Sch-ray/KUMA-DIV/Shell_Model/Image/IMG_3518.jpg

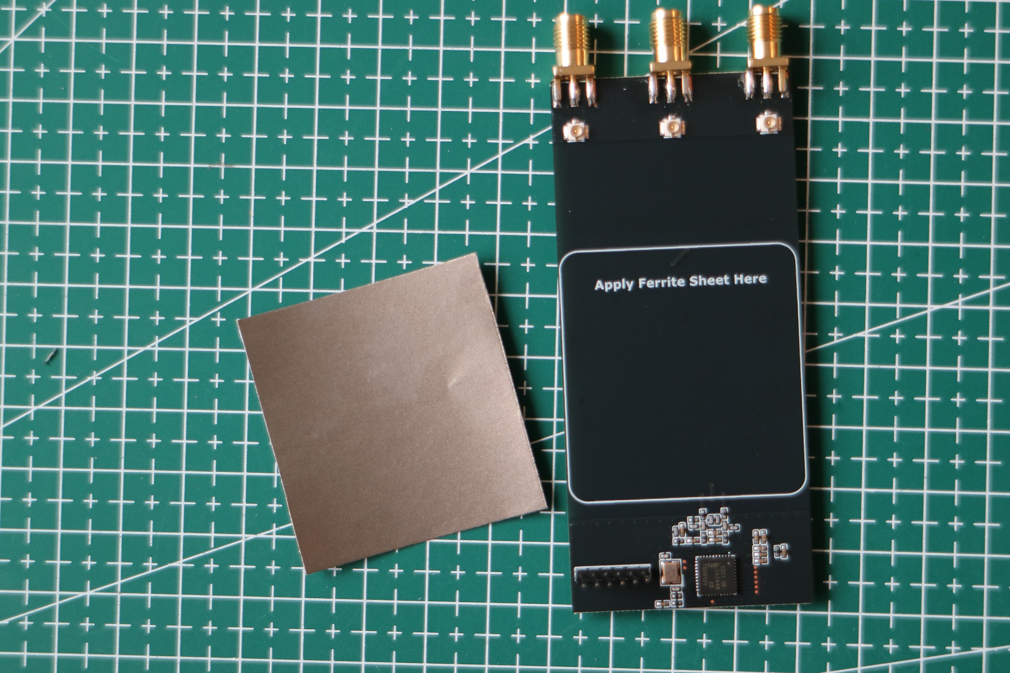
Shell_Model/Image/IMG_3518.jpg
