Sch-ray/KUMA-DIV/Software/ESP32-DIV/icon.h

// 'navigate_right2', 16x16px
const unsigned char bitmap_icon_navigate_right2 [] PROGMEM = {
	0x00, 0x00, 0x00, 0x00, 0x30, 0x80, 0x79, 0xc0, 0x3d, 0xe0, 0x1e, 0xf0, 0x0f, 0x7c, 0x07, 0xbe, 
	0x07, 0xbe, 0x0f, 0x7c, 0x1e, 0xf0, 0x3d, 0xe0, 0x79, 0xc0, 0x30, 0x80, 0x00, 0x00, 0x00, 0x00
};
// 'navigate_right', 16x16px
const unsigned char bitmap_icon_navigate_right [] PROGMEM = {
	0x00, 0x00, 0x00, 0x00, 0x06, 0x00, 0x0f, 0x00, 0x07, 0x80, 0x03, 0xc0, 0x01, 0xe0, 0x00, 0xf0, 
	0x00, 0xf0, 0x01, 0xe0, 0x03, 0xc0, 0x07, 0x80, 0x0f, 0x00, 0x06, 0x00, 0x00, 0x00, 0x00, 0x00
};
// 'navigate_left', 16x16px
const unsigned char bitmap_icon_navigate_left [] PROGMEM = {
	0x00, 0x00, 0x00, 0x00, 0x00, 0x60, 0x00, 0xf0, 0x01, 0xe0, 0x03, 0xc0, 0x07, 0x80, 0x0f, 0x00, 
	0x0f, 0x00, 0x07, 0x80, 0x03, 0xc0, 0x01, 0xe0, 0x00, 0xf0, 0x00, 0x60, 0x00, 0x00, 0x00, 0x00
};
// 'navigate_left2', 16x16px
const unsigned char bitmap_icon_navigate_left2 [] PROGMEM = {
	0x00, 0x00, 0x00, 0x00, 0x01, 0x0c, 0x03, 0x9e, 0x07, 0xbc, 0x0f, 0x78, 0x3e, 0xf0, 0x7d, 0xe0, 
	0x7d, 0xe0, 0x3e, 0xf0, 0x0f, 0x78, 0x07, 0xbc, 0x03, 0x9e, 0x01, 0x0c, 0x00, 0x00, 0x00, 0x00
};
// 'rfid_chip', 16x16px
const unsigned char bitmap_icon_rfid_chip [] PROGMEM = {
	0x00, 0x00, 0x00, 0x00, 0x3f, 0xfc, 0x20, 0x04, 0x2f, 0xf4, 0x28, 0x14, 0x2b, 0xd4, 0x2b, 0xd4, 
	0x2b, 0xd4, 0x2b, 0xd4, 0x2a, 0x14, 0x29, 0xf4, 0x24, 0x04, 0x33, 0xfc, 0x00, 0x00, 0x00, 0x00
};
// 'about', 16x16px
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
  0x00, 0x00, 0x00, 0x00, 0x00, 0x00, 0x00, 0x04, 0x21, 0x10, 0x01, 0x98, 0x00, 0x00, 0x00, 0x00, 
  0x00, 0x00, 0x00, 0x00, 0x60, 0x80, 0x80, 0x08, 0x20, 0x00, 0x00, 0x00, 0x00, 0x00, 0x00, 0x00, 
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
};
