Sch-ray/KUMA-DIV/Software/ESP32-DIV/utils.cpp

#include <SD.h>
#include <SPI.h>
#include <algorithm>
#include <cmath>
#include <vector>
#include "driver/gpio.h"
#include "Touchscreen.h"
#include "config.h"
#include "freertos/FreeRTOS.h"
#include "freertos/task.h"
#include "icon.h"
#include "gps.h"
#include "shared.h"
#include "utils.h"

bool has_ip5306 = false;

bool notificationVisible = false;
static bool notificationHasSave = false;
static int notifX, notifY, notifWidth, notifHeight;
static int closeButtonX, closeButtonY, closeButtonSize = 16;
static int okButtonX, okButtonY, okButtonWidth = 84, okButtonHeight = 24;
static int saveButtonX, saveButtonY, saveButtonWidth = 84, saveButtonHeight = 24;

static char s_notifTitleCache[64];
static char s_notifMsgCache[400];
static bool s_notifShowSaveCache = false;

/** Wrapped line count for modal text (font 1, size 1 — must match draw path). */
static int countWrappedNotifLines(const String& msgIn, int innerPixelW) {
  tft.setTextFont(1);
  tft.setTextSize(1);
  String msg = msgIn;
  msg.trim();
  int lines = 0;
  while (msg.length() > 0 && lines < 48) {
    int lineEnd = msg.length();
    while (lineEnd > 0 && tft.textWidth(msg.substring(0, lineEnd)) > innerPixelW) {
      lineEnd--;
    }
    if (lineEnd <= 0) {
      ++lines;
      break;
    }
    if (lineEnd < msg.length()) {
      const int lastSpace = msg.substring(0, lineEnd).lastIndexOf(' ');
      if (lastSpace > 0) {
        lineEnd = lastSpace;
      }
    }
    ++lines;
    msg = msg.substring(lineEnd);
    msg.trim();
  }
  return lines;
}

static size_t decodeObfTo(char* out, size_t outSize, const uint8_t* in, size_t inLen, uint8_t key) {
  if (!out || outSize == 0) return 0;
  size_t n = inLen;
  if (n > outSize - 1) n = outSize - 1;
  for (size_t i = 0; i < n; ++i) out[i] = (char)(in[i] ^ key);
  out[n] = '\0';
  return n;
}

void tftPrintObf(const uint8_t* data, size_t len, uint8_t key) {
  char buf[96];
  decodeObfTo(buf, sizeof(buf), data, len, key);
  tft.print(buf);
}

void tftPrintlnObf(const uint8_t* data, size_t len, uint8_t key) {
  char buf[96];
  decodeObfTo(buf, sizeof(buf), data, len, key);
  tft.println(buf);
}

void serialPrintObf(const uint8_t* data, size_t len, bool newline, uint8_t key) {
  char buf[128];
  decodeObfTo(buf, sizeof(buf), data, len, key);
  if (newline) Serial.println(buf);
  else Serial.print(buf);
}

static inline bool inRect(int x, int y, int rx, int ry, int rw, int rh) {
  return x >= rx && x < (rx + rw) && y >= ry && y < (ry + rh);
}

static void drawNotificationInternal(const char* title, const char* message, bool showSave) {
    snprintf(s_notifTitleCache, sizeof(s_notifTitleCache), "%s", title ? title : "");
    snprintf(s_notifMsgCache, sizeof(s_notifMsgCache), "%s", message ? message : "");
    s_notifShowSaveCache = showSave;
    notificationHasSave = showSave;

    const int scrW = tft.width();
    const int scrH = tft.height();
    notifWidth = (scrW > 232) ? 224 : (scrW - 16);
    if (notifWidth < 160) {
        notifWidth = 160;
    }

    const int messageBoxWidth = notifWidth - 10;
    const int innerTextW = messageBoxWidth - 6;
    const int lineH = 12;
    const int footH = showSave ? 40 : 30;
    const int topBand = 25;

    tft.setTextFont(1);
    tft.setTextSize(1);
    String msgProbe = message ? String(message) : String("");
    msgProbe.trim();
    int lineCount = countWrappedNotifLines(msgProbe, innerTextW);
    if (lineCount < 2) {
        lineCount = 2;
    }
    const int maxLinesByScreen = (scrH - topBand - footH - 14) / lineH;
    int useLines = lineCount;
    if (useLines > maxLinesByScreen) {
        useLines = maxLinesByScreen > 2 ? maxLinesByScreen : 2;
    }

    const int messageBoxHeight = 8 + useLines * lineH;
    notifHeight = topBand + messageBoxHeight + footH;
    if (notifHeight > scrH - 8) {
        notifHeight = scrH - 8;
        const int availBody = notifHeight - topBand - footH;
        useLines = (availBody - 8) / lineH;
        if (useLines < 2) {
            useLines = 2;
        }
    }
    notifX = (scrW - notifWidth) / 2;
    notifY = (scrH - notifHeight) / 2;
    if (notifY < 4) {
        notifY = 4;
    }

    tft.fillRect(notifX, notifY, notifWidth, notifHeight, LIGHT_GRAY);
    tft.drawRect(notifX, notifY, notifWidth, notifHeight, DARK_GRAY);
    tft.fillRect(notifX, notifY, notifWidth, 20, BLUE);

    tft.setTextColor(WHITE, BLUE);
    tft.setTextSize(1);
    tft.setCursor(notifX + 6, notifY + 5);
    tft.print(title);

    closeButtonX = notifX + notifWidth - closeButtonSize - 6;
    closeButtonY = notifY + 3;
    tft.fillRect(closeButtonX, closeButtonY, closeButtonSize, closeButtonSize, RED);
    tft.setTextColor(WHITE, RED);
    tft.setCursor(closeButtonX + 5, closeButtonY + 4);
    tft.print("X");

    int messageBoxX = notifX + 5;
    int messageBoxY = notifY + 25;
    const int messageBoxDrawH = notifHeight - topBand - footH;
    tft.fillRect(messageBoxX, messageBoxY, messageBoxWidth, messageBoxDrawH, WHITE);
    tft.setTextColor(BLACK, WHITE);

    {
      const int maxY = messageBoxY + messageBoxDrawH - lineH;
      String msg = message ? String(message) : String("");
      msg.trim();
      int cursorX = messageBoxX + 3;
      int cursorY = messageBoxY + 4;
      while (msg.length() > 0 && cursorY <= maxY) {
        int lineEnd = msg.length();
        while (lineEnd > 0 && tft.textWidth(msg.substring(0, lineEnd)) > innerTextW) {
          lineEnd--;
        }
        if (lineEnd <= 0) {
          break;
        }
        if (lineEnd < msg.length()) {
          int lastSpace = msg.substring(0, lineEnd).lastIndexOf(' ');
          if (lastSpace > 0) {
            lineEnd = lastSpace;
          }
        }
        tft.setCursor(cursorX, cursorY);
        tft.print(msg.substring(0, lineEnd));
        msg = msg.substring(lineEnd);
        msg.trim();
        cursorY += lineH;
      }

      if (msg.length() > 0) {
        tft.setCursor(cursorX, maxY);
        tft.print("...");
      }
    }

    int btnY = notifY + notifHeight - 25;
    if (showSave) {
      okButtonWidth = 72;
      saveButtonWidth = 72;
      okButtonHeight = saveButtonHeight = 20;
      okButtonX = notifX + 10;
      saveButtonX = notifX + notifWidth - 10 - saveButtonWidth;
      okButtonY = saveButtonY = btnY;

      tft.fillRect(okButtonX, okButtonY, okButtonWidth, okButtonHeight, GRAY);
      tft.drawRect(okButtonX, okButtonY, okButtonWidth, okButtonHeight, DARK_GRAY);
      tft.drawLine(okButtonX, okButtonY, okButtonX + okButtonWidth, okButtonY, WHITE);
      tft.drawLine(okButtonX, okButtonY, okButtonX, okButtonY + okButtonHeight, WHITE);
      tft.setTextColor(BLACK, GRAY);
      tft.setCursor(okButtonX + 28, okButtonY + 5);
      tft.print("OK");

      tft.fillRect(saveButtonX, saveButtonY, saveButtonWidth, saveButtonHeight, GREEN);
      tft.drawRect(saveButtonX, saveButtonY, saveButtonWidth, saveButtonHeight, DARK_GRAY);
      tft.drawLine(saveButtonX, saveButtonY, saveButtonX + saveButtonWidth, saveButtonY, WHITE);
      tft.drawLine(saveButtonX, saveButtonY, saveButtonX, saveButtonY + saveButtonHeight, WHITE);
      tft.setTextColor(BLACK, GREEN);
      tft.setCursor(saveButtonX + 18, saveButtonY + 5);
      tft.print("SAVE");
    } else {
      okButtonWidth = 72;
      okButtonHeight = 20;
      okButtonX = notifX + (notifWidth - okButtonWidth) / 2;
      okButtonY = btnY;
      tft.fillRect(okButtonX, okButtonY, okButtonWidth, okButtonHeight, GRAY);
      tft.drawRect(okButtonX, okButtonY, okButtonWidth, okButtonHeight, DARK_GRAY);
      tft.drawLine(okButtonX, okButtonY, okButtonX + okButtonWidth, okButtonY, WHITE);
      tft.drawLine(okButtonX, okButtonY, okButtonX, okButtonY + okButtonHeight, WHITE);
      tft.setTextColor(BLACK, GRAY);
      tft.setCursor(okButtonX + 28, okButtonY + 5);
      tft.print("OK");
    }

    notificationVisible = true;
}

void showNotificationActions(const char* title, const char* message, bool showSave) {
    drawNotificationInternal(title, message, showSave);
}

void showNotification(const char* title, const char* message) {
    drawNotificationInternal(title, message, false);
}

void hideNotification() {
    applyThemeToPalette(settings().theme);
    tft.fillRect(notifX, notifY, notifWidth, notifHeight, UI_BG);
    notificationVisible = false;
}

bool isNotificationVisible() { return notificationVisible; }

void notificationRedrawIfVisible() {
    if (!notificationVisible) {
        return;
    }
    drawNotificationInternal(s_notifTitleCache, s_notifMsgCache, s_notifShowSaveCache);
}

NotificationAction notificationHandleTouch(int x, int y) {
  if (!notificationVisible) return NotificationAction::None;

  if (inRect(x, y, closeButtonX, closeButtonY, closeButtonSize, closeButtonSize)) {
    hideNotification();
    return NotificationAction::Close;
  }
  if (inRect(x, y, okButtonX, okButtonY, okButtonWidth, okButtonHeight)) {
    hideNotification();
    return NotificationAction::Ok;
  }
  if (notificationHasSave && inRect(x, y, saveButtonX, saveButtonY, saveButtonWidth, saveButtonHeight)) {
    hideNotification();
    return NotificationAction::Save;
  }
  return NotificationAction::None;
}

void printWrappedText(int x, int y, int maxWidth, const char* text) {
    String message = text;
    int cursorX = x, cursorY = y;

    while (message.length() > 0) {
        int lineEnd = message.length();

        while (tft.textWidth(message.substring(0, lineEnd)) > maxWidth) {
            lineEnd--;
        }

        if (lineEnd < message.length()) {
            int lastSpace = message.substring(0, lineEnd).lastIndexOf(' ');
            if (lastSpace > 0) lineEnd = lastSpace;
        }

        tft.setCursor(cursorX, cursorY);
        tft.print(message.substring(0, lineEnd));

        message = message.substring(lineEnd);
        message.trim();

        cursorY += 15;
    }
}

namespace FeatureUI {

#ifndef FEATURE_TEXT
#define FEATURE_TEXT ORANGE
#endif

static inline uint16_t btnFill(ButtonStyle style, bool pressed, bool disabled) {
  if (disabled) return UI_LINE;
  if (pressed)  return UI_FG;
  switch (style) {
    case ButtonStyle::Primary:   return FEATURE_TEXT;
    case ButtonStyle::Secondary: return UI_FG;
    case ButtonStyle::Danger:    return UI_WARN;
  }
  return UI_FG;
}

static inline uint16_t btnBorder(ButtonStyle style, bool disabled) {
  if (disabled) return UI_LINE;
  switch (style) {
    case ButtonStyle::Primary:   return FEATURE_TEXT;
    case ButtonStyle::Secondary: return FEATURE_TEXT;
    case ButtonStyle::Danger:    return UI_WARN;
  }
  return FEATURE_TEXT;
}

static inline uint16_t btnText(ButtonStyle style, bool disabled) {
  if (disabled) return UI_TEXT;

  switch (style) {
    case ButtonStyle::Secondary: return UI_ICON;
    case ButtonStyle::Primary:
    case ButtonStyle::Danger:    return FEATURE_BG;
  }
  return UI_ICON;
}

void drawFooterBg() {

  tft.fillRect(0, tft.height() - FOOTER_H, tft.width(), FOOTER_H, FEATURE_BG);
}

void drawButtonRect(int x, int y, int w, int h,
                    const char* label,
                    ButtonStyle style,
                    bool pressed,
                    bool disabled,
                    uint8_t font) {
  if (!label) label = "";
  int r = h / 2;
  if (r > 6) r = 6;
  if (r < 0) r = 0;
  uint16_t fill = btnFill(style, pressed, disabled);
  uint16_t edge = btnBorder(style, disabled);
  uint16_t txt  = btnText(style, disabled);

  tft.fillRoundRect(x, y, w, h, r, fill);
  tft.drawRoundRect(x, y, w, h, r, edge);

  tft.setTextDatum(MC_DATUM);
  tft.setTextColor(txt, fill);

  tft.drawString(label, x + w/2, y + h/2, font);

  tft.setTextDatum(TL_DATUM);
  tft.setTextFont(1);
  tft.setTextSize(1);
  tft.setTextColor(UI_TEXT, FEATURE_BG);
}

void layoutFooter3(Button (&btns)[3],
                   const char* l0, ButtonStyle s0,
                   const char* l1, ButtonStyle s1,
                   const char* l2, ButtonStyle s2,
                   bool d0, bool d1, bool d2) {
  int availW = tft.width() - 2*PAD_X;
  int w = (availW - 2*GAP_X) / 3;
  int y = tft.height() - FOOTER_H + (FOOTER_H - BTN_H)/2;
  int x0 = PAD_X;
  int x1 = x0 + w + GAP_X;
  int x2 = x1 + w + GAP_X;
  btns[0] = {(int16_t)x0,(int16_t)y,(int16_t)w,(int16_t)BTN_H,l0,s0,d0};
  btns[1] = {(int16_t)x1,(int16_t)y,(int16_t)w,(int16_t)BTN_H,l1,s1,d1};
  btns[2] = {(int16_t)x2,(int16_t)y,(int16_t)w,(int16_t)BTN_H,l2,s2,d2};
}

void layoutFooter2(Button (&btns)[2],
                   const char* l0, ButtonStyle s0,
                   const char* l1, ButtonStyle s1,
                   bool d0, bool d1) {
  int availW = tft.width() - 2*PAD_X;
  int w = (availW - GAP_X) / 2;
  int y = tft.height() - FOOTER_H + (FOOTER_H - BTN_H)/2;
  int x0 = PAD_X;
  int x1 = x0 + w + GAP_X;
  btns[0] = {(int16_t)x0,(int16_t)y,(int16_t)w,(int16_t)BTN_H,l0,s0,d0};
  btns[1] = {(int16_t)x1,(int16_t)y,(int16_t)w,(int16_t)BTN_H,l1,s1,d1};
}

void layoutFooter4(Button (&btns)[4],
                   const char* l0, ButtonStyle s0,
                   const char* l1, ButtonStyle s1,
                   const char* l2, ButtonStyle s2,
                   const char* l3, ButtonStyle s3,
                   bool d0, bool d1, bool d2, bool d3) {
  int availW = tft.width() - 2*PAD_X;
  int w = (availW - 3*GAP_X) / 4;
  int y = tft.height() - FOOTER_H + (FOOTER_H - BTN_H)/2;
  int x0 = PAD_X;
  int x1 = x0 + w + GAP_X;
  int x2 = x1 + w + GAP_X;
  int x3 = x2 + w + GAP_X;
  btns[0] = {(int16_t)x0,(int16_t)y,(int16_t)w,(int16_t)BTN_H,l0,s0,d0};
  btns[1] = {(int16_t)x1,(int16_t)y,(int16_t)w,(int16_t)BTN_H,l1,s1,d1};
  btns[2] = {(int16_t)x2,(int16_t)y,(int16_t)w,(int16_t)BTN_H,l2,s2,d2};
  btns[3] = {(int16_t)x3,(int16_t)y,(int16_t)w,(int16_t)BTN_H,l3,s3,d3};
}

void layoutFooter1(Button& btn, const char* label, ButtonStyle style, bool disabled) {
  int x = PAD_X;
  int w = tft.width() - 2*PAD_X;
  int y = tft.height() - FOOTER_H + (FOOTER_H - BTN_H)/2;
  btn = {(int16_t)x,(int16_t)y,(int16_t)w,(int16_t)BTN_H,label,style,disabled};
}

void layoutFooter5(Button (&btns)[5],
                   const char* l0, ButtonStyle s0,
                   const char* l1, ButtonStyle s1,
                   const char* l2, ButtonStyle s2,
                   const char* l3, ButtonStyle s3,
                   const char* l4, ButtonStyle s4,
                   bool d0, bool d1, bool d2, bool d3, bool d4) {
  int availW = tft.width() - 2*PAD_X;
  int w = (availW - 4*GAP_X) / 5;
  int y = tft.height() - FOOTER_H + (FOOTER_H - BTN_H)/2;
  int x0 = PAD_X;
  int x1 = x0 + w + GAP_X;
  int x2 = x1 + w + GAP_X;
  int x3 = x2 + w + GAP_X;
  int x4 = x3 + w + GAP_X;
  btns[0] = {(int16_t)x0,(int16_t)y,(int16_t)w,(int16_t)BTN_H,l0,s0,d0};
  btns[1] = {(int16_t)x1,(int16_t)y,(int16_t)w,(int16_t)BTN_H,l1,s1,d1};
  btns[2] = {(int16_t)x2,(int16_t)y,(int16_t)w,(int16_t)BTN_H,l2,s2,d2};
  btns[3] = {(int16_t)x3,(int16_t)y,(int16_t)w,(int16_t)BTN_H,l3,s3,d3};
  btns[4] = {(int16_t)x4,(int16_t)y,(int16_t)w,(int16_t)BTN_H,l4,s4,d4};
}

int hit(const Button* btns, int n, int x, int y) {
  for (int i = 0; i < n; ++i) {
    const auto& b = btns[i];
    if (x >= b.x && x <= (b.x + b.w) && y >= b.y && y <= (b.y + b.h)) return i;
  }
  return -1;
}

}

unsigned long lastStatusBarUpdate = 0;
const int STATUS_BAR_UPDATE_INTERVAL = 2000;
float lastBatteryVoltage = 0.0;
bool sdCardPresent = false;
bool lastSdCardState = false;

static TaskHandle_t statusBarTaskHandle = nullptr;
static volatile bool statusBarDirty = true;
static constexpr uint32_t kStatusBarWardBlinkHalfMs = 900;

void requestStatusBarRedraw() {
  statusBarDirty = true;
}

const float R1 = 100000.0;
const float R2 = 100000.0;

float readBatteryVoltage()
{
  static bool adcInitialized = false;

  if (!adcInitialized)
  {
    analogSetPinAttenuation(BATTERY_ADC_PIN, ADC_11db);
    adcInitialized = true;
  }

  const int sampleCount = 16;
  uint32_t sum = 0;

  for (int i = 0; i < sampleCount; i++)
  {
    sum += analogReadMilliVolts(BATTERY_ADC_PIN);
    delayMicroseconds(500);
  }

  float avgMv = sum / (float)sampleCount;

  return (avgMv / 1000.0f) * 2.0f;
}

float readInternalTemperature() {
  float temperature = temperatureRead();
  return temperature;
}

void updateSdCardStatus() {

#ifdef SD_CD
  bool cardDetected = !digitalRead(SD_CD);
#else
  bool cardDetected = true;
#endif

  if (cardDetected != lastSdCardState) {
    sdCardPresent = cardDetected;
    lastSdCardState = cardDetected;

    Serial.println(sdCardPresent ? "SD Card detected" : "SD Card removed");
    requestStatusBarRedraw();
  }
}

static bool statusBarBatteryMeaningfulChange(int newPct, int oldPct, bool force) {
  if (force || oldPct == -1) {
    return true;
  }
  if (newPct <= 25 || oldPct <= 25) {
    return newPct != oldPct;
  }
  const int d = newPct - oldPct;
  return (d >= 3 || d <= -3);
}

static int statusBarTempBand(float t) {
  if (fabs(static_cast<double>(t) - 53.33) < 0.51) {
    return 1;
  }
  if (t > 55.f) {
    return 2;
  }
  return 0;
}

void drawStatusBar(float batteryVoltage, bool forceUpdate, bool bottomSeparator) {
  static int lastBatteryPercentage = -1;
  static int lastWifiHalf          = -100000;
  static int lastBleHalf           = -100000;
  static int lastTempBand          = -100;
  static int lastSdSnap            = -1;
  static bool lastWardGpsIcon      = false;
  static uint32_t lastWardBlinkPhase = 0;

  /*
  int batteryPercentage = ::map(batteryVoltage * 100, 300, 420, 0, 100);
  */
  /*调用IP5306*/
  int batteryPercentage = 0;
  if (has_ip5306) {
    Wire.beginTransmission(IP5306_ADDR);
    Wire.write(0x78);
    if (Wire.endTransmission(false) == 0 && Wire.requestFrom(IP5306_ADDR, 1)) {
      switch (Wire.read() & 0xF0) {
        case 0xE0: batteryPercentage = 25;break;
        case 0xC0: batteryPercentage = 50;break;
        case 0x80: batteryPercentage = 75;break;
        case 0x00: batteryPercentage = 100;break;
        default: batteryPercentage = 0;break;
      }
    }
  }

  batteryPercentage = constrain(batteryPercentage, 0, 100);

  int wifiDevices = 0;
  int bleDevices  = 0;

  wifiDevices = WifiScan::getLastCount();
  bleDevices  = BleScan::getLastCount();

  const int wifiHalf = wifiDevices / 2;
  const int bleHalf  = bleDevices / 2;

  const bool wardGpsIcon = GpsWardriver::statusBarGpsIconActive();
  const uint32_t wardBlinkPhase =
      wardGpsIcon ? (millis() / kStatusBarWardBlinkHalfMs) : 0u;
  const bool wardSatVisible =
      wardGpsIcon && ((wardBlinkPhase & 1u) == 0u);

  const float internalTemp = readInternalTemperature();
  const int tempBand         = statusBarTempBand(internalTemp);
  const int sdSnap           = sdCardPresent ? 1 : 0;

  const bool battCh =
      statusBarBatteryMeaningfulChange(batteryPercentage, lastBatteryPercentage, forceUpdate);
  const bool wardBlinkOnly =
      !forceUpdate && wardGpsIcon && lastWardGpsIcon &&
      (wardBlinkPhase != lastWardBlinkPhase) && !battCh && wifiHalf == lastWifiHalf &&
      bleHalf == lastBleHalf && tempBand == lastTempBand && sdSnap == lastSdSnap;

  if (wardBlinkOnly) {
    constexpr int kBarH   = 20;
    constexpr int kY      = 4;
    constexpr int kIconY  = kY - 2;
    constexpr int kIconW  = 16;
    constexpr int kGap    = 3;
    constexpr int kBleIx  = 130;
    constexpr int kBleDrawX = kBleIx + 25;
    const int wardGpsX    = kBleDrawX - kGap - kIconW;
    if (wardSatVisible) {
      tft.drawBitmap(wardGpsX, kIconY, bitmap_icon_satellite, kIconW, kIconW, TFT_ORANGE);
    } else {
      tft.fillRect(wardGpsX, kIconY, kIconW, kIconW, UI_LABLE);
    }
    if (bottomSeparator) {
      tft.drawFastHLine(0, kBarH - 1, tft.width(), TFT_WHITE);
    }
    lastWardBlinkPhase = wardBlinkPhase;
    return;
  }

  if (battCh || wifiHalf != lastWifiHalf || bleHalf != lastBleHalf || tempBand != lastTempBand ||
      sdSnap != lastSdSnap || wardGpsIcon != lastWardGpsIcon ||
      (wardGpsIcon && wardBlinkPhase != lastWardBlinkPhase) || forceUpdate) {
    int barHeight = 20;
    int x = 7;
    int y = 4;

    tft.fillRect(0, 0, tft.width(), barHeight, UI_LABLE);

    tft.drawRoundRect(x, y, 22, 10, 2, TFT_WHITE);
    tft.fillRect(x + 22, y + 3, 2, 4, TFT_WHITE);

    int batteryLevelWidth = ::map(batteryPercentage, 0, 100, 0, 20);
    uint16_t batteryColor = (batteryPercentage > 20) ? GREEN : TFT_RED;
    tft.fillRoundRect(x + 2, y + 2, batteryLevelWidth, 6, 1, batteryColor);

    tft.setCursor(x + 30, y + 2);
    tft.setTextColor(GREEN, UI_LABLE);
    tft.setTextFont(1);
    tft.setTextSize(1);
    tft.print(String(batteryPercentage) + "%");

    const int iconW         = 16;
    const int gap           = 3;
    const int wifiBarsWidth = 24;

    const int bleIconX      = 130;
    const int bleTextX      = bleIconX + iconW + gap;
    const int wifiBarsX     = bleTextX + 12 + gap;
    const int tempIconX     = wifiBarsX + wifiBarsWidth + gap;
    const int sdIconX       = tempIconX + iconW + gap;
    int iconY               = y - 2;

    int clearWidth = tft.width() - bleIconX;
    tft.fillRect(bleIconX, 0, clearWidth, barHeight, UI_LABLE);

    const int bleDrawX = bleIconX + 25;
    if (wardSatVisible) {
      const int wardGpsX = bleDrawX - gap - iconW;
      tft.drawBitmap(wardGpsX, iconY, bitmap_icon_satellite, iconW, iconW, TFT_ORANGE);
    }

    uint16_t wifiColor = (wifiDevices > 0) ? GREEN : TFT_WHITE;
    uint16_t bleColor  = (bleDevices  > 0) ? TFT_CYAN  : TFT_WHITE;

    int wifiStrength = 0;
    if (wifiDevices > 0) {

      wifiStrength = constrain(::map(wifiDevices, 0, 15, 0, 100), 0, 100);
    }

    int wifiX = wifiBarsX + 10;
    int wifiY = y + 11;

    for (int i = 0; i < 4; i++) {
      const int sigBarH = (i + 1) * 3;
      const int barWidth  = 4;
      const int barX      = wifiX + i * 6;

      if (wifiStrength > i * 25) {
        tft.fillRoundRect(barX, wifiY - sigBarH, barWidth, sigBarH, 1, GREEN);
      } else {
        tft.drawRoundRect(barX, wifiY - sigBarH, barWidth, sigBarH, 1, TFT_WHITE);
      }
    }

    tft.drawBitmap(bleIconX + 25, iconY, bitmap_icon_ble, 16, 16, bleColor);
    tft.setTextColor(bleColor, UI_LABLE);

    if (internalTemp == 53.33f) {
      tft.drawBitmap(tempIconX + 10, y - 2, bitmap_icon_temp, 16, 16, TFT_YELLOW);
    } else if (internalTemp > 55) {
      tft.drawBitmap(tempIconX + 10, y - 2, bitmap_icon_temp, 16, 16, TFT_RED);
    } else {
      tft.drawBitmap(tempIconX + 10, y - 2, bitmap_icon_temp, 16, 16, GREEN);
    }

    if (sdCardPresent) {
      tft.drawBitmap(sdIconX + 10, y - 2, bitmap_icon_sdcard, 16, 16, GREEN);
    } else {
      tft.drawBitmap(sdIconX + 10, y - 2, bitmap_icon_nullsdcard, 16, 16, TFT_RED);
    }

    if (bottomSeparator) {
      tft.drawFastHLine(0, barHeight - 1, tft.width(), TFT_WHITE);
    }

    lastBatteryPercentage = batteryPercentage;
    lastWifiHalf          = wifiHalf;
    lastBleHalf           = bleHalf;
    lastTempBand          = tempBand;
    lastSdSnap            = sdSnap;
    lastWardGpsIcon       = wardGpsIcon;
    lastWardBlinkPhase    = wardGpsIcon ? wardBlinkPhase : 0u;
  }
}

static void statusBarTask(void* ) {
  static int prevBattPct    = -1;
  static int prevWifiHalf   = -100000;
  static int prevBleHalf    = -100000;
  static int prevTempBand   = -100;
  static int prevSdSnap     = -1;
  static bool prevWardIcon  = false;
  static uint32_t prevWardPhase = 0;

  for (;;) {
    updateSdCardStatus();
    const float v = readBatteryVoltage();
    currentBatteryVoltage = v;

    const int pct = constrain(::map((int)(v * 100.f), 300, 420, 0, 100), 0, 100);
    const int wifi  = WifiScan::getLastCount();
    const int ble   = BleScan::getLastCount();
    const int wifiH = wifi / 2;
    const int bleH  = ble / 2;
    const int tBand = statusBarTempBand(readInternalTemperature());
    const int sdSn  = sdCardPresent ? 1 : 0;
    const bool ward = GpsWardriver::statusBarGpsIconActive();
    const uint32_t wPh = ward ? (millis() / kStatusBarWardBlinkHalfMs) : 0u;

    bool need = false;
    if (statusBarBatteryMeaningfulChange(pct, prevBattPct, false)) {
      need = true;
    }
    if (wifiH != prevWifiHalf || bleH != prevBleHalf) {
      need = true;
    }
    if (tBand != prevTempBand || sdSn != prevSdSnap) {
      need = true;
    }
    if (ward != prevWardIcon) {
      need = true;
    }
    if (ward && wPh != prevWardPhase) {
      need = true;
    }

    if (need) {
      statusBarDirty = true;
      prevBattPct     = pct;
      prevWifiHalf    = wifiH;
      prevBleHalf     = bleH;
      prevTempBand    = tBand;
      prevSdSnap      = sdSn;
      prevWardIcon    = ward;
      prevWardPhase   = ward ? wPh : 0u;
    }

    vTaskDelay(pdMS_TO_TICKS(400));
  }
}

void startStatusBarTask() {
  if (statusBarTaskHandle != nullptr) return;
  xTaskCreatePinnedToCore(
    statusBarTask,
    "statusBar",
    2048,
    nullptr,
    1,
    &statusBarTaskHandle,
    0
  );
}

void pauseBackgroundRadioTasks() {
  GpsWardriver::stopBackgroundIfRunning();
}

void updateStatusBar() {

  if (statusBarTaskHandle != nullptr) {
    if (statusBarDirty) {
      drawStatusBar(currentBatteryVoltage, false);
      statusBarDirty = false;
    }
    return;
  }

  const unsigned long currentMillis = millis();
  const bool wardOn = GpsWardriver::statusBarGpsIconActive();
  static uint32_t s_noTaskLastWardPhase = UINT32_MAX;
  const uint32_t wardPh =
      wardOn ? (currentMillis / kStatusBarWardBlinkHalfMs) : 0u;
  const bool wardBlinkTick =
      wardOn && (s_noTaskLastWardPhase == UINT32_MAX || wardPh != s_noTaskLastWardPhase);
  if (wardOn) {
    s_noTaskLastWardPhase = wardPh;
  } else {
    s_noTaskLastWardPhase = UINT32_MAX;
  }

  if (currentMillis - lastStatusBarUpdate > STATUS_BAR_UPDATE_INTERVAL || wardBlinkTick) {
    float batteryVoltage = readBatteryVoltage();
    updateSdCardStatus();
    currentBatteryVoltage = batteryVoltage;
    drawStatusBar(batteryVoltage, false);
    lastBatteryVoltage = batteryVoltage;
    lastStatusBarUpdate = currentMillis;
  }
}

#if HAS_PCF8574_BUTTONS
static uint8_t s_pcf8574Addr = 0;

uint8_t getPcf8574Address() {
  return s_pcf8574Addr;
}

bool initPcf8574Buttons() {
  // Prevent I2C bus hangs (no ACK / missing pull-ups) from tripping the task WDT
  // and rebooting right after the intro on classic ESP32.
  Wire.begin();
  Wire.setTimeOut(50);

  pcf.pinMode(BTN_UP, INPUT_PULLUP);
  pcf.pinMode(BTN_DOWN, INPUT_PULLUP);
  pcf.pinMode(BTN_LEFT, INPUT_PULLUP);
  pcf.pinMode(BTN_RIGHT, INPUT_PULLUP);
  pcf.pinMode(BTN_SELECT, INPUT_PULLUP);

#if PCF8574_AUTO_DETECT
  for (uint8_t addr = PCF8574_ADDR_MIN; addr <= PCF8574_ADDR_MAX; addr++) {
    yield();
    if (pcf.begin(addr)) {
      s_pcf8574Addr = addr;
      Serial.printf("[PCF8574] auto-detected at 0x%02X\n", addr);
      break;
    }
  }
  if (s_pcf8574Addr == 0) {
    Serial.println("[PCF8574] not found (scanned 0x20-0x27)");
    return false;
  }
#else
  if (!pcf.begin(PCF8574_I2C_ADDR)) {
    Serial.printf("[PCF8574] not found at fixed address 0x%02X\n", PCF8574_I2C_ADDR);
    return false;
  }
  s_pcf8574Addr = PCF8574_I2C_ADDR;
  Serial.printf("[PCF8574] using fixed address 0x%02X\n", s_pcf8574Addr);
#endif

  return true;
}
#else
uint8_t getPcf8574Address() {
  return 0;
}

bool initPcf8574Buttons() {
  return false;
}
#endif

#if TOUCH_SHARES_TFT_SPI
#if defined(CONFIG_IDF_TARGET_ESP32S3)
static SPIClass s_sdSpi(FSPI);
#elif defined(CONFIG_IDF_TARGET_ESP32)
static SPIClass s_sdSpi(VSPI);
#else
static SPIClass s_sdSpi(FSPI);
#endif
#endif

/** Tracks whether SD.begin() currently owns a live mount on the shared SPI bus. */
static bool s_sdFsMounted = false;

/** GPIO CS that last mounted SD (-1 = unknown). Tried first to avoid long SD.begin on wrong CS. */
static int8_t s_sdLastGoodCs = -1;

/** After a failed mount on classic ESP32, do not keep retrying (SD.begin can WDT). */
static bool s_sdMountGaveUp = false;

void sdRetryMount() {
  s_sdMountGaveUp = false;
}

/** Deselect every other SPI slave that shares the SD bus so none holds MISO. */
static void sdRaiseCsPin(int pin) {
  if (pin < 0) {
    return;
  }
  pinMode(pin, OUTPUT);
  digitalWrite(pin, HIGH);
}

static void sdReleaseOtherChipSelects() {
#if defined(CC1101_CS)
  sdRaiseCsPin(CC1101_CS);
#endif
#if defined(PN532_SS)
  sdRaiseCsPin(PN532_SS);
#endif
#if defined(CSN_PIN_1)
  sdRaiseCsPin(CSN_PIN_1);
#endif
#if defined(CSN_PIN_2)
  sdRaiseCsPin(CSN_PIN_2);
#endif
#if defined(CSN_PIN_3)
  sdRaiseCsPin(CSN_PIN_3);
#endif
  // Scanner bit-bangs CE/CSN on these pins; keep CE low / CSN high after leaving.
#if defined(CE_PIN_3)
  pinMode(CE_PIN_3, OUTPUT);
  digitalWrite(CE_PIN_3, LOW);
#endif
}

void sdSpiInit() {
#if defined(SD_SCLK) && defined(SD_MISO) && defined(SD_MOSI) && defined(SD_CS)
#if TOUCH_SHARES_TFT_SPI
  s_sdSpi.begin(SD_SCLK, SD_MISO, SD_MOSI, SD_CS);
#else
  // On ESP32-S3 (v2), RFID bitbang remaps these pins — reset before reclaim.
  // On classic ESP32 (v1), SD often shares SPI with TFT_eSPI; gpio_reset_pin
  // after tft.init() can WDT/reboot during boot SD mount.
#if BOARD_HAS_ESP32S3
  gpio_reset_pin((gpio_num_t)SD_SCLK);
  gpio_reset_pin((gpio_num_t)SD_MISO);
  gpio_reset_pin((gpio_num_t)SD_MOSI);
  gpio_reset_pin((gpio_num_t)SD_CS);
#endif
  SPI.begin(SD_SCLK, SD_MISO, SD_MOSI, SD_CS);
  SPI.setDataMode(SPI_MODE0);
  SPI.setBitOrder(MSBFIRST);
  SPI.setFrequency(4000000);
#endif
#endif
}

bool sdMountChipSelect(uint8_t cs) {
#if TOUCH_SHARES_TFT_SPI
  return SD.begin(cs, s_sdSpi, 4000000);
#else
  return SD.begin(cs, SPI, 4000000);
#endif
}

void initSDCard() {

#ifdef SD_CD
  pinMode(SD_CD, INPUT_PULLUP);
#endif

#if !BOARD_HAS_ESP32S3
  // Classic ESP32: raise CS only. Full SD.begin is deferred — boot mount was
  // rebooting right after the intro ("3 sd").
#if defined(SD_CS)
  pinMode(SD_CS, OUTPUT);
  digitalWrite(SD_CS, HIGH);
#endif
  sdReleaseOtherChipSelects();
  // Block auto-mount from settingsLoad / status bar until an SD feature asks.
  s_sdMountGaveUp = true;
  updateSdCardStatus();
  return;
#else
  restoreSdAfterSharedSpi();
  updateSdCardStatus();
#endif
}

static bool sdPinIsOkForSdMount(uint8_t pin) {
#if defined(SD_CS)
  if (pin == SD_CS) {
    return true;
  }
#endif
#if defined(SD_CS_PIN)
#if defined(CC1101_CS)
  if (SD_CS_PIN != CC1101_CS && pin == SD_CS_PIN) {
    return true;
  }
#else
  if (pin == SD_CS_PIN) {
    return true;
  }
#endif
#endif
  return false;
}

static void sdAddPinUnique(uint8_t* pins, int* nTry, uint8_t p) {
  if (!sdPinIsOkForSdMount(p)) {
    return;
  }
  for (int j = 0; j < *nTry; j++) {
    if (pins[j] == p) {
      return;
    }
  }
  if (*nTry < 3) {
    pins[(*nTry)++] = p;
  }
}

/** SPI must already be SD wiring. Returns true if SD.begin succeeded. */
static bool sdTryBeginOrder() {
  uint8_t tryPins[3];
  int nTry = 0;
  if (s_sdLastGoodCs >= 0) {
    sdAddPinUnique(tryPins, &nTry, (uint8_t)s_sdLastGoodCs);
  }
#if defined(SD_CS)
  sdAddPinUnique(tryPins, &nTry, SD_CS);
#endif
#if defined(SD_CS_PIN)
#if defined(CC1101_CS)
  if (SD_CS_PIN != CC1101_CS) {
    sdAddPinUnique(tryPins, &nTry, SD_CS_PIN);
  }
#else
  sdAddPinUnique(tryPins, &nTry, SD_CS_PIN);
#endif
#endif
  for (int i = 0; i < nTry; i++) {
    if (sdMountChipSelect(tryPins[i])) {
      s_sdLastGoodCs = (int8_t)tryPins[i];
      return true;
    }
  }
  s_sdLastGoodCs = -1;
  return false;
}

/** Soft remount: keep current SPI pinmux. Safe while CC1101/nRF24 still need the bus
 *  (same SCK/MISO/MOSI as SD on DIV V2). Only raises other chip-selects and remounts FatFS. */
static bool sdRemountSoft() {
  sdReleaseOtherChipSelects();

#if defined(SD_SCLK) && defined(SD_MISO) && defined(SD_MOSI) && defined(SD_CS)
#if TOUCH_SHARES_TFT_SPI
  s_sdSpi.begin(SD_SCLK, SD_MISO, SD_MOSI, SD_CS);
#else
  // Do not SPI.end()/gpio_reset here — that tears down CC1101 after SubGHz Init.
  SPI.begin(SD_SCLK, SD_MISO, SD_MOSI, SD_CS);
  SPI.setDataMode(SPI_MODE0);
  SPI.setBitOrder(MSBFIRST);
#endif
#endif

  SD.end();
  s_sdFsMounted = false;
  delay(2);
  if (sdTryBeginOrder()) {
    s_sdFsMounted = true;
#if !TOUCH_SHARES_TFT_SPI
    // SD.begin() often leaves the bus at 16–40 MHz; CC1101 cannot use that.
    SPI.setFrequency(4000000);
#endif
    return true;
  }
  return false;
}

bool isSDCardAvailable() {
#ifdef SD_CD
  updateSdCardStatus();
  if (!sdCardPresent) {
    return false;
  }
#endif

  // FatFS "exists(/)" can stay true after another feature stole the SPI bus.
  // cardType() actually talks to the card and catches a dead mount.
  if (s_sdFsMounted) {
    if (SD.cardType() != CARD_NONE) {
      return true;
    }
    s_sdFsMounted = false;
    SD.end();
  }

#if !BOARD_HAS_ESP32S3
  if (s_sdMountGaveUp) {
    return false;
  }
#endif

  // Prefer a soft remount so SubGHz (CC1101 on the same SPI pins) stays alive.
  if (sdRemountSoft()) {
    return true;
  }

  // Soft failed — pins may still be in RFID bitbang / Scanner remapped state.
  // Only do the destructive reclaim when no radio feature owns the bus.
  if (!feature_active) {
    restoreSdAfterSharedSpi();
#if !BOARD_HAS_ESP32S3
    if (!s_sdFsMounted) {
      s_sdMountGaveUp = true;
      Serial.println("[sd] mount failed — will not retry until reboot");
    }
#endif
    return s_sdFsMounted;
  }
  return false;
}

void holdSdInactiveOnSharedSpi() {
#if defined(SD_CS)
  pinMode(SD_CS, OUTPUT);
  digitalWrite(SD_CS, HIGH);
#endif
#if !TOUCH_SHARES_TFT_SPI
  SPI.setDataMode(SPI_MODE0);
  SPI.setBitOrder(MSBFIRST);
  SPI.setFrequency(4000000);
#endif
}

void reclaimSharedSpiBus() {
  // Reset pinmux after RFID bitbang / Scanner remaps, but do NOT SD.begin().
  // Mounting SD here is what broke SubGHz: SD.begin raises SPI clock and parks
  // the card on the same MISO line CC1101 needs.
  sdReleaseOtherChipSelects();
#if defined(SD_CS)
  pinMode(SD_CS, OUTPUT);
  digitalWrite(SD_CS, HIGH);
#endif
#if defined(CC1101_CS)
  pinMode(CC1101_CS, OUTPUT);
  digitalWrite(CC1101_CS, HIGH);
#endif
#if defined(PN532_SS)
  pinMode(PN532_SS, OUTPUT);
  digitalWrite(PN532_SS, HIGH);
#endif

  SD.end();
  s_sdFsMounted = false;

#if !TOUCH_SHARES_TFT_SPI
  SPI.end();
#if BOARD_HAS_ESP32S3
#if defined(SD_SCLK) && defined(SD_MISO) && defined(SD_MOSI)
  gpio_reset_pin((gpio_num_t)SD_SCLK);
  gpio_reset_pin((gpio_num_t)SD_MISO);
  gpio_reset_pin((gpio_num_t)SD_MOSI);
#endif
  // PN532 software-SPI may have bitbanged these (on DIV V2 MOSI/MISO are
  // swapped vs SD/CC1101). Reset them even when they overlap SD pins.
#if defined(PN532_SCK)
  gpio_reset_pin((gpio_num_t)PN532_SCK);
#endif
#if defined(PN532_MISO)
  gpio_reset_pin((gpio_num_t)PN532_MISO);
#endif
#if defined(PN532_MOSI)
  gpio_reset_pin((gpio_num_t)PN532_MOSI);
#endif
#if defined(PN532_SS)
  gpio_reset_pin((gpio_num_t)PN532_SS);
  pinMode(PN532_SS, OUTPUT);
  digitalWrite(PN532_SS, HIGH);
#endif
#if defined(SD_CS)
  gpio_reset_pin((gpio_num_t)SD_CS);
  pinMode(SD_CS, OUTPUT);
  digitalWrite(SD_CS, HIGH);
#endif
#if defined(CC1101_CS)
  gpio_reset_pin((gpio_num_t)CC1101_CS);
  pinMode(CC1101_CS, OUTPUT);
  digitalWrite(CC1101_CS, HIGH);
#endif
#endif // BOARD_HAS_ESP32S3
#if defined(SD_SCLK) && defined(SD_MISO) && defined(SD_MOSI) && defined(SD_CS)
#if defined(CC1101_SCK) && defined(CC1101_MISO) && defined(CC1101_MOSI) && defined(CC1101_CS)
  // Prefer CC1101 CS as SPI SS — same data pins as SD on DIV V2, but matches
  // what ELECHOUSE SpiStart() will bind on the next Init().
  SPI.begin(CC1101_SCK, CC1101_MISO, CC1101_MOSI, CC1101_CS);
#else
  SPI.begin(SD_SCLK, SD_MISO, SD_MOSI, SD_CS);
#endif
  SPI.setDataMode(SPI_MODE0);
  SPI.setBitOrder(MSBFIRST);
  SPI.setFrequency(4000000);
#endif
#else
#if defined(SD_SCLK) && defined(SD_MISO) && defined(SD_MOSI) && defined(SD_CS)
  s_sdSpi.begin(SD_SCLK, SD_MISO, SD_MOSI, SD_CS);
#endif
#endif
  delay(2);
}

void restoreSdAfterSharedSpi() {
  // Full reclaim + remount for menu/SD features after leaving SPI radios.
  reclaimSharedSpiBus();
  delay(5);
  if (sdTryBeginOrder()) {
    s_sdFsMounted = true;
#if !TOUCH_SHARES_TFT_SPI
    SPI.setFrequency(4000000);
#endif
  }
  requestStatusBarRedraw();
}

void loading(int frameDelay, uint16_t color, int16_t x, int16_t y, int repeats, bool center) {
  int16_t bitmapWidth = 100;
  int16_t bitmapHeight = 120;
  int16_t logoX = x;
  int16_t logoY = y;

  if (center) {
    int16_t screenWidth = tft.width();
    int16_t screenHeight = tft.height();
    logoX = (screenWidth - bitmapWidth) / 2;
    logoY = (screenHeight - bitmapHeight) / 2;
  }

  const unsigned char* bitmaps[] = {
    bitmap_icon_skull_loading_1,
    bitmap_icon_skull_loading_2,
    bitmap_icon_skull_loading_3,
    bitmap_icon_skull_loading_4,
    bitmap_icon_skull_loading_5,
    bitmap_icon_skull_loading_6,
    bitmap_icon_skull_loading_7,
    bitmap_icon_skull_loading_8,
    bitmap_icon_skull_loading_9,
    bitmap_icon_skull_loading_10
  };
  const int numFrames = 10;

  for (int r = 0; r < repeats; r++) {
    for (int i = 0; i < numFrames; i++) {
      tft.fillRect(logoX, logoY, bitmapWidth, bitmapHeight, TFT_BLACK);
      tft.drawBitmap(logoX, logoY, bitmaps[i], bitmapWidth, bitmapHeight, color);
      delay(frameDelay);
    }
  }
}

void displayLogo(uint16_t color, int displayTime) {
  int16_t bitmapWidth = 150;
  int16_t bitmapHeight = 150;
  int16_t screenWidth = tft.width();
  int16_t screenHeight = tft.height();
  int16_t logoX = (screenWidth - bitmapWidth) / 2;
  int16_t logoY = (screenHeight - bitmapHeight) / 2 - 20;

  tft.fillRect(logoX, logoY, bitmapWidth, bitmapHeight, TFT_BLACK);
  tft.drawBitmap(logoX, logoY, bitmap_icon_cifer, bitmapWidth, bitmapHeight, color);

  tft.setTextColor(color);
  tft.setTextFont(1);

  tft.setTextSize(2);
  int16_t textX = screenWidth / 3.5;
  int16_t textY = logoY + bitmapHeight + 10;
  tft.setCursor(textX, textY);
  tftPrintObf(OBF_PN, sizeof(OBF_PN));

  tft.setTextSize(1);
  textX = screenWidth / 3.5;
  textY += 20;
  tft.setCursor(textX, textY);
  tft.print("by ");
  tftPrintObf(OBF_DN, sizeof(OBF_DN));

  textX = screenWidth / 2.5;
  textY += 50;
  tft.setCursor(textX, textY);
  // Version is intentionally NOT obfuscated.
  tft.print(ESP32DIV_VERSION);

  Serial.println("==================================");
  serialPrintObf(OBF_PN, sizeof(OBF_PN), true);
  Serial.print("Developed by: "); serialPrintObf(OBF_DN, sizeof(OBF_DN), true);
  // Version is intentionally NOT obfuscated.
  Serial.print("Version:      "); Serial.println(ESP32DIV_VERSION);
  Serial.print("Contact:      "); serialPrintObf(OBF_EM, sizeof(OBF_EM), true);
  Serial.print("GitHub:       "); serialPrintObf(OBF_GH, sizeof(OBF_GH), true);
  Serial.print("Website:      "); serialPrintObf(OBF_WB, sizeof(OBF_WB), true);
  Serial.println("==================================");

  delay(displayTime);
}

namespace Terminal {

#define TEXT_HEIGHT 16
#define BOT_FIXED_AREA 0
#define TOP_FIXED_AREA 86
#define DISPLAY_WIDTH 240
#define DISPLAY_HEIGHT 320
#define SCREEN_WIDTH 240
#define SCREENHEIGHT 320

static bool uiDrawn = false;

uint16_t yStart = TOP_FIXED_AREA;
uint16_t yArea = DISPLAY_HEIGHT - TOP_FIXED_AREA - BOT_FIXED_AREA;
uint16_t yDraw = DISPLAY_HEIGHT - BOT_FIXED_AREA - TEXT_HEIGHT;

uint16_t xPos = 0;

byte data = 0;

boolean change_colour = 1;
boolean selected = 1;
boolean terminalActive = true;

int blank[19];

long baudRates[] = {9600, 19200, 38400, 57600, 115200};
byte baudIndex = 0;

static int terminalContentBottom() {
  return featureHasTouchNavBar() ? (int)touchNavContentBottomY() : DISPLAY_HEIGHT;
}

static int terminalBotFixedArea() {
  const int bottom = terminalContentBottom();
  return (bottom < DISPLAY_HEIGHT) ? (DISPLAY_HEIGHT - bottom) : BOT_FIXED_AREA;
}

static void terminalUpdateNavLabels() {
  if (!featureHasTouchNavBar()) {
    return;
  }
  setTouchNavLabels("Exit", nullptr, terminalActive ? "Pause" : "Active", nullptr, "Baud");
  redrawTouchButtonBar();
}

static void terminalCycleBaud() {
  if (terminalActive) {
    terminalActive = false;
    terminalUpdateNavLabels();
    return;
  }
  baudIndex = (baudIndex + 1) % 5;
  Serial.end();
  delay(100);
  Serial.begin(baudRates[baudIndex]);
  tft.fillRect(0, 37, DISPLAY_WIDTH, 16, ORANGE);
  tft.setTextColor(TFT_WHITE, TFT_WHITE);
  String baudMsg = " Serial Terminal - " + String(baudRates[baudIndex]) + " baud ";
  tft.drawCentreString(baudMsg, DISPLAY_WIDTH / 2, 37, 2);
  delay(10);
}

static void terminalSetActive(bool active) {
  terminalActive = active;
  delay(10);
  tft.fillRect(0, 37, DISPLAY_WIDTH, 16, ORANGE);
  tft.setTextColor(TFT_WHITE, TFT_WHITE);
  if (active) {
    tft.drawCentreString(" Serial Terminal Active ", DISPLAY_WIDTH / 2, 37, 2);
  } else {
    String baudMsg = " Serial Terminal - " + String(baudRates[baudIndex]) + " baud ";
    tft.drawCentreString(baudMsg, DISPLAY_WIDTH / 2, 37, 2);
  }
  terminalUpdateNavLabels();
}

static void terminalHandleNavButtons() {
  if (!featureHasTouchNavBar()) {
    return;
  }
  if (isTouchNavButtonPressedEdge(BTN_LEFT)) {
    feature_exit_requested = true;
    return;
  }
  if (isTouchNavButtonPressedEdge(BTN_RIGHT)) {
    terminalCycleBaud();
    return;
  }
  if (isTouchNavButtonPressedEdge(BTN_SELECT)) {
    terminalSetActive(!terminalActive);
  }
}
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
